jpconstantineau/NRF52-Board/BlueMicro1.x/Images/01.jpg

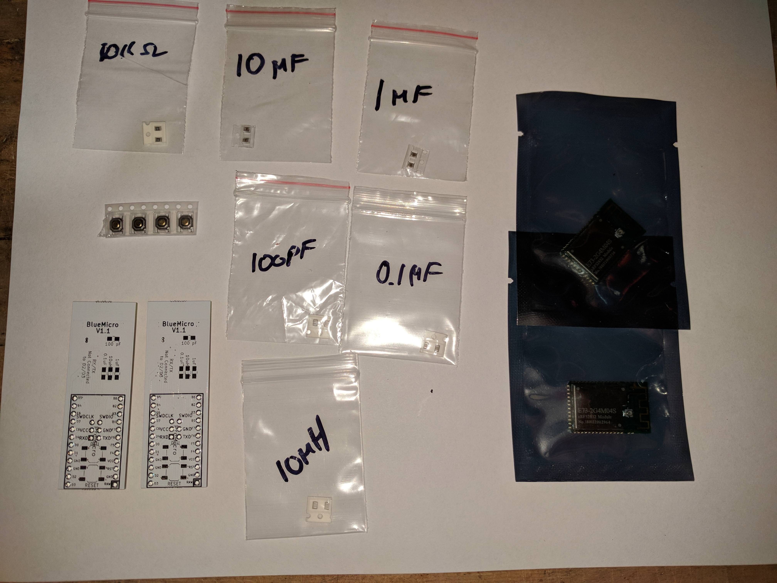
BlueMicro1.x/Images/01.jpg
