jpconstantineau/NRF52-Board/BlueMicro1.x/Images/02.jpg

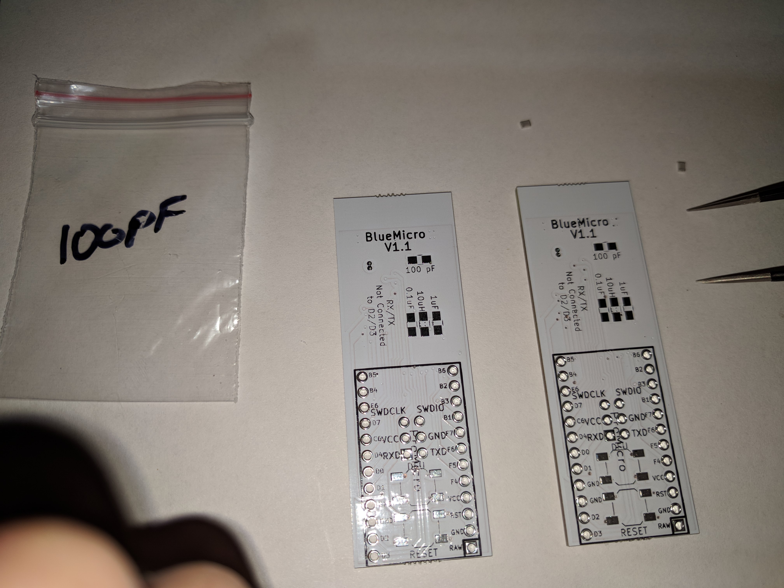
BlueMicro1.x/Images/02.jpg
