jpconstantineau/NRF52-Board/BlueMicro1.x/Images/03.jpg

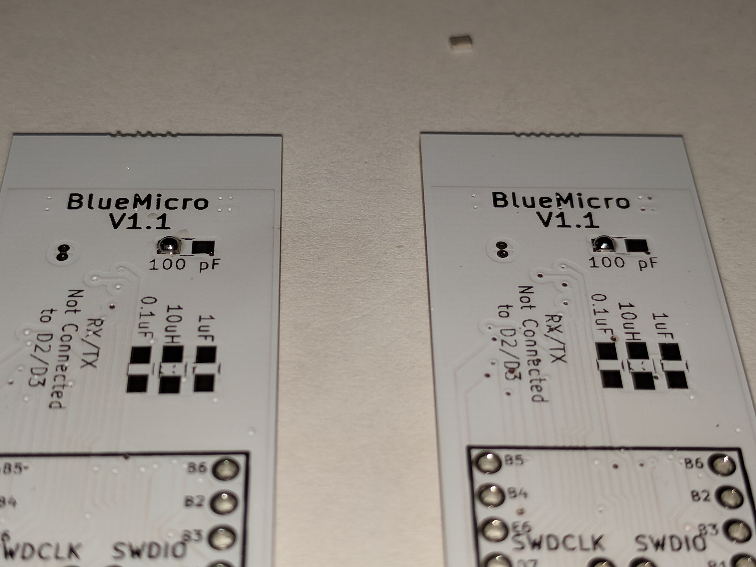
BlueMicro1.x/Images/03.jpg
