jpconstantineau/NRF52-Board/BlueMicro1.x/Images/04.jpg

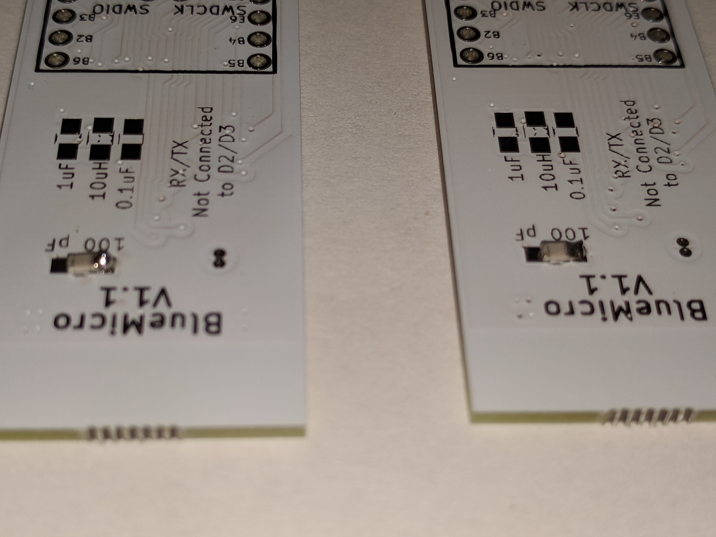
BlueMicro1.x/Images/04.jpg
