jpconstantineau/NRF52-Board/BlueMicro1.x/Images/05.jpg

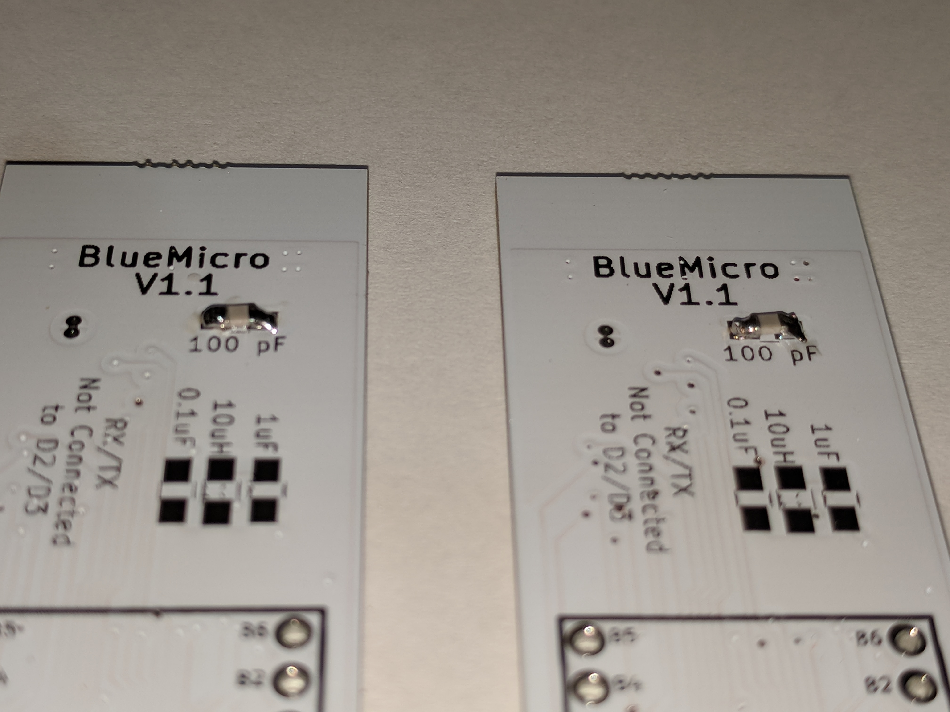
BlueMicro1.x/Images/05.jpg
