jpconstantineau/NRF52-Board/BlueMicro1.x/Images/06.jpg

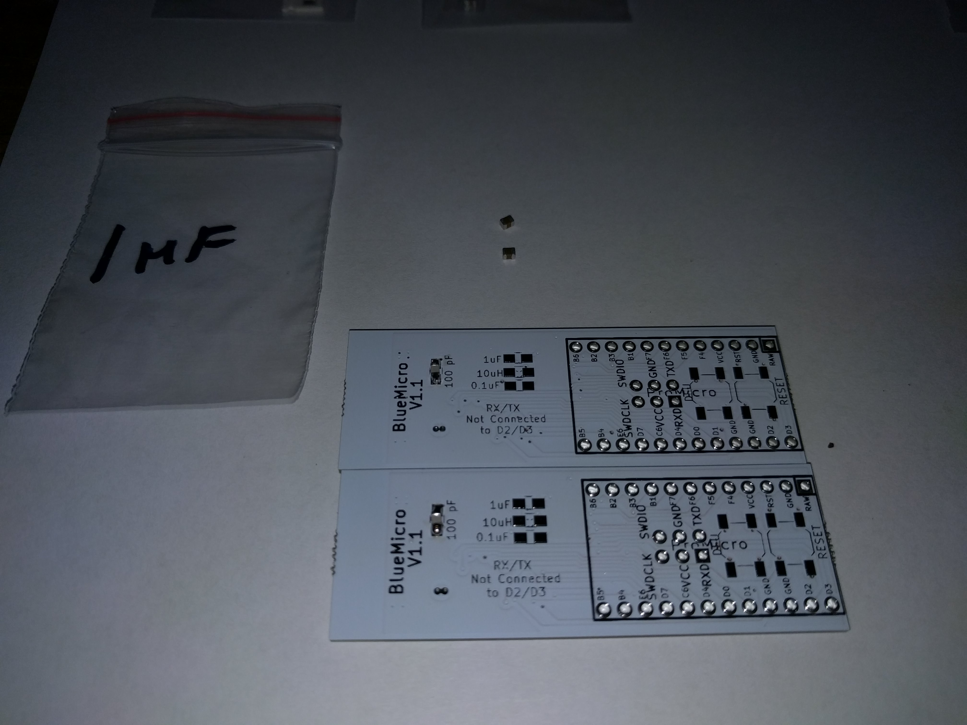
BlueMicro1.x/Images/06.jpg
