jpconstantineau/NRF52-Board/BlueMicro1.x/Images/07.jpg

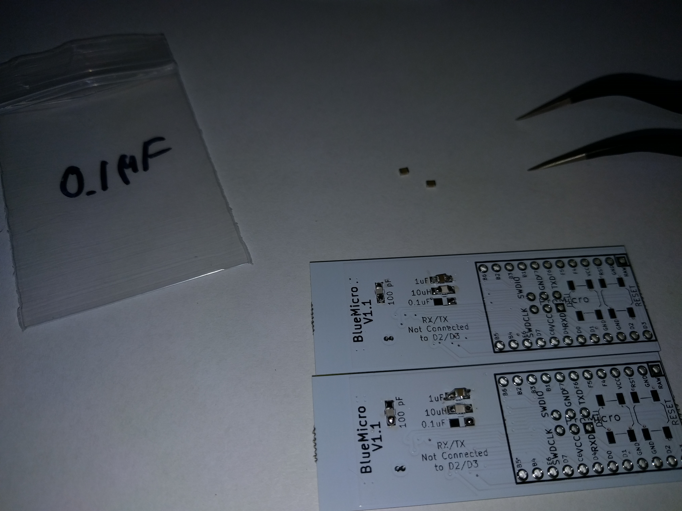
BlueMicro1.x/Images/07.jpg
