jpconstantineau/NRF52-Board/BlueMicro1.x/Images/08.jpg

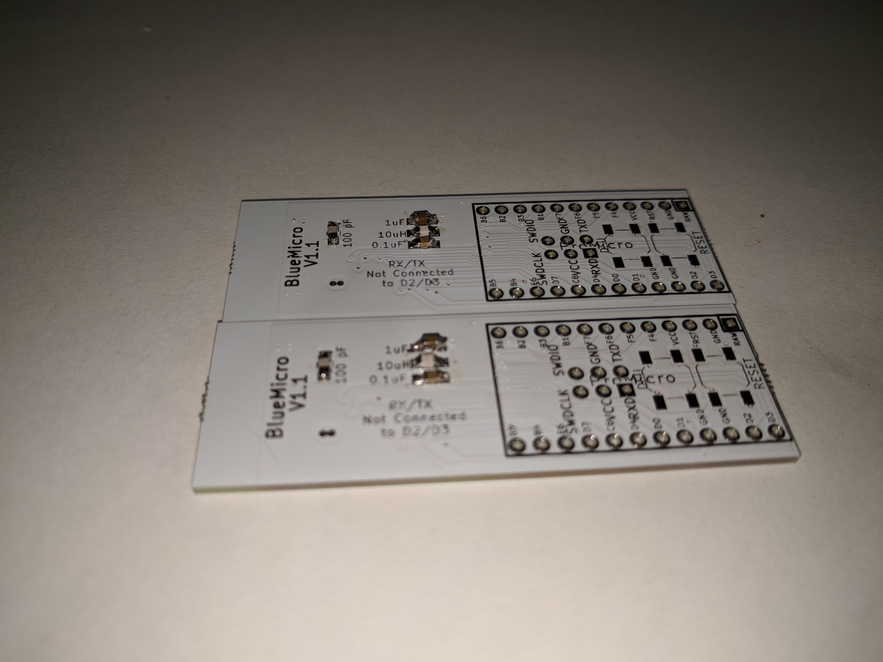
BlueMicro1.x/Images/08.jpg
