jpconstantineau/NRF52-Board/BlueMicro1.x/Images/09.jpg

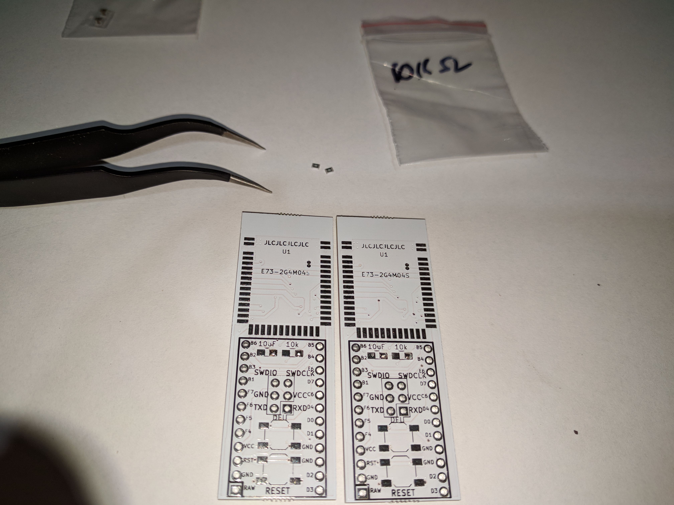
BlueMicro1.x/Images/09.jpg
