jpconstantineau/NRF52-Board/BlueMicro1.x/Images/10.jpg

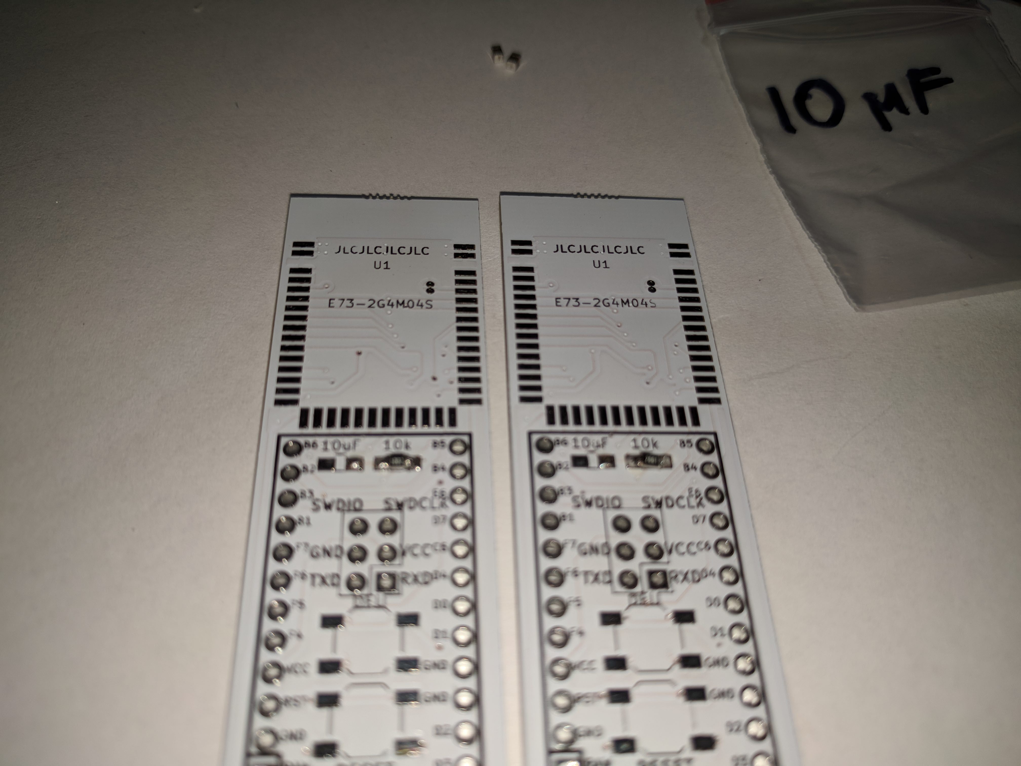
BlueMicro1.x/Images/10.jpg
