jpconstantineau/NRF52-Board/BlueMicro1.x/Images/11.jpg

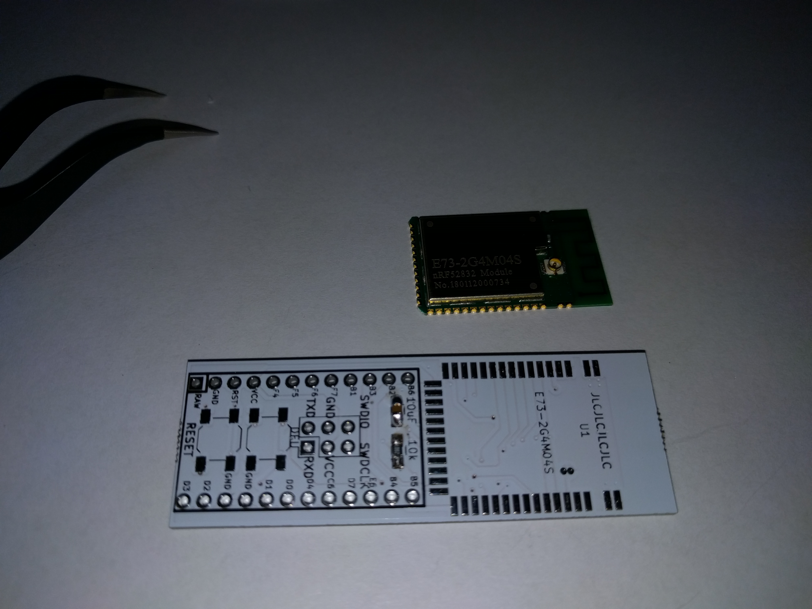
BlueMicro1.x/Images/11.jpg
