jpconstantineau/NRF52-Board/BlueMicro1.x/Images/12.jpg

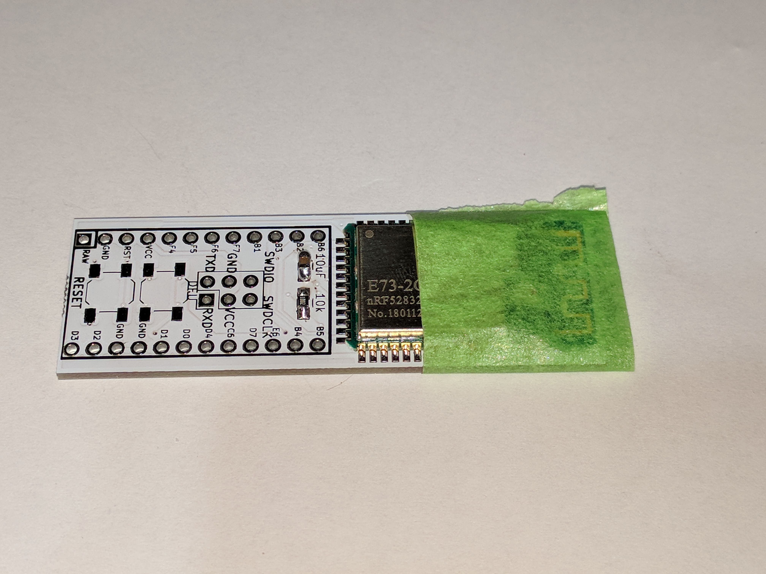
BlueMicro1.x/Images/12.jpg
