jpconstantineau/NRF52-Board/BlueMicro1.x/Images/13.jpg

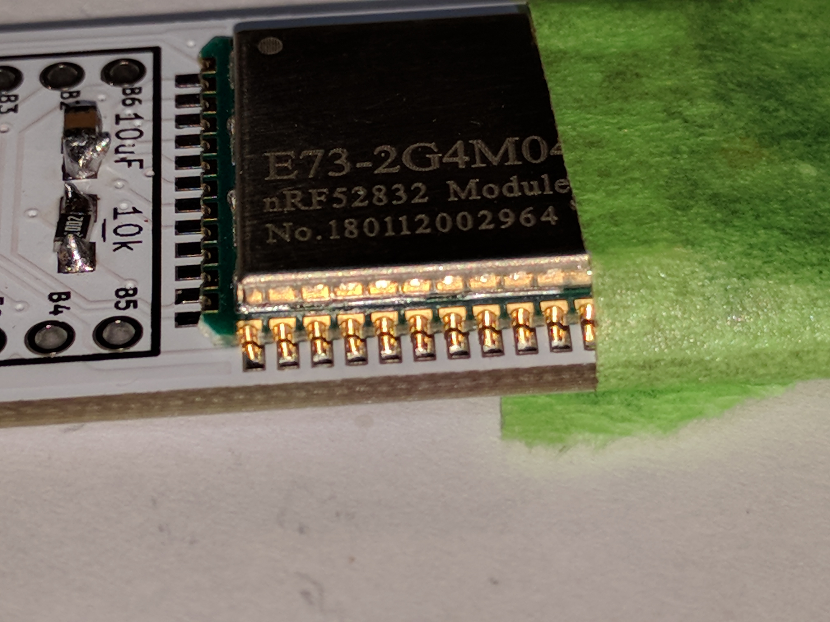
BlueMicro1.x/Images/13.jpg
