jpconstantineau/NRF52-Board/BlueMicro1.x/Images/14.jpg

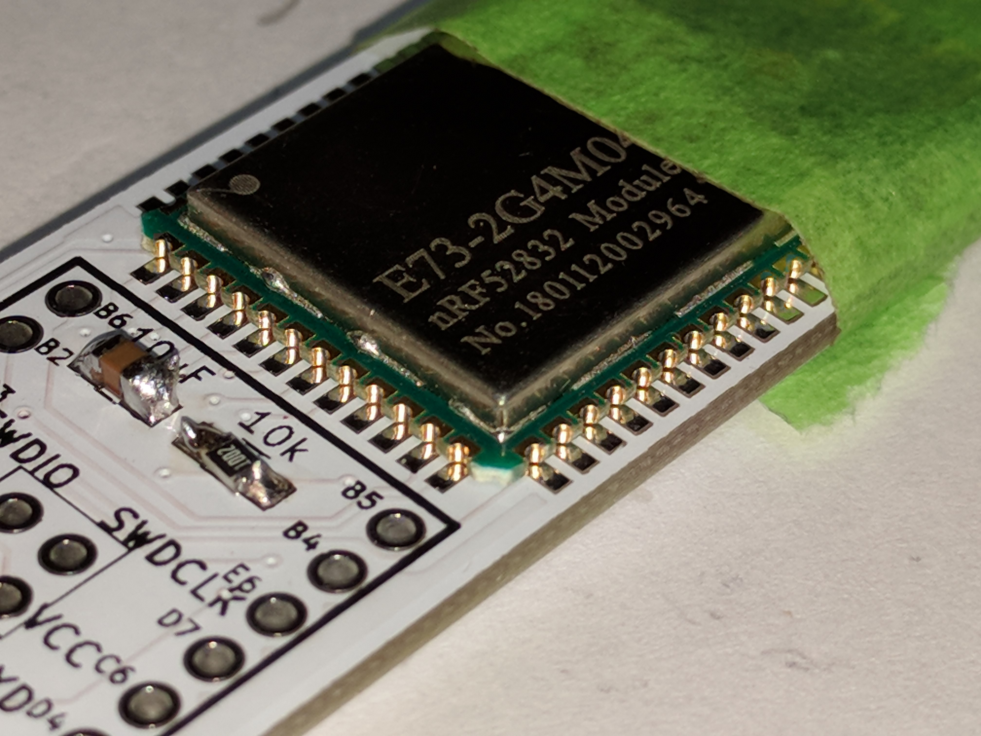
BlueMicro1.x/Images/14.jpg
