jpconstantineau/NRF52-Board/BlueMicro1.x/Images/15.jpg

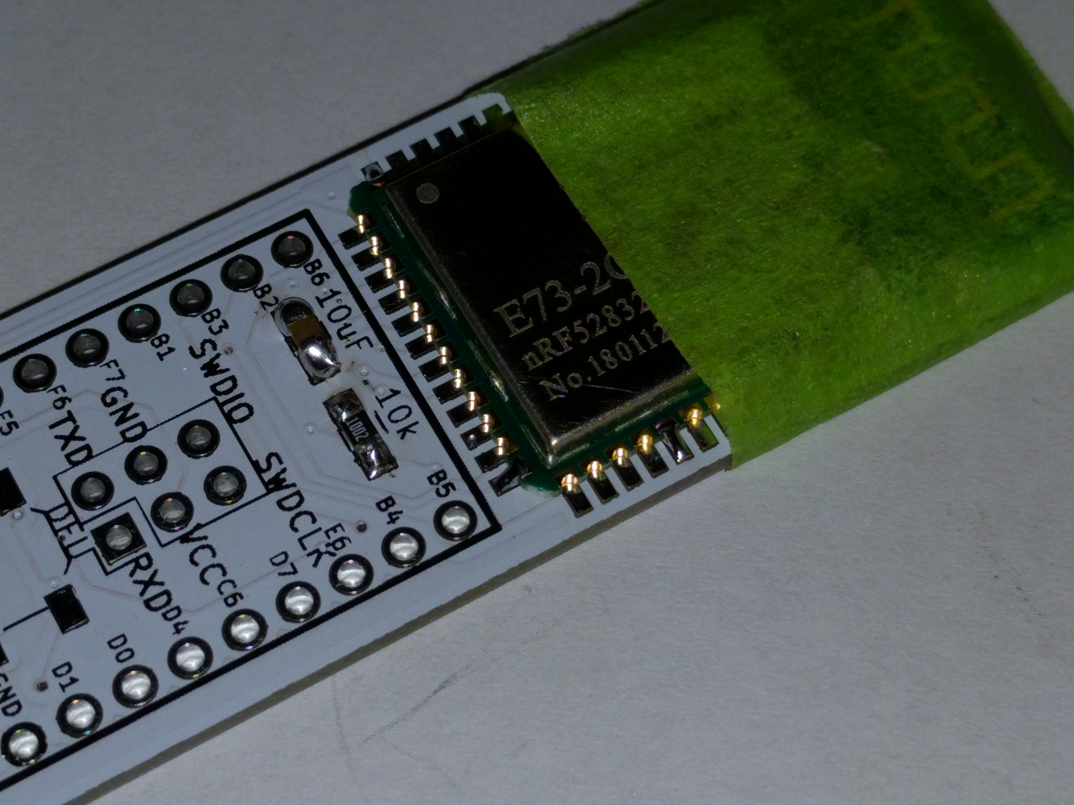
BlueMicro1.x/Images/15.jpg
