jpconstantineau/NRF52-Board/BlueMicro1.x/Images/16.jpg

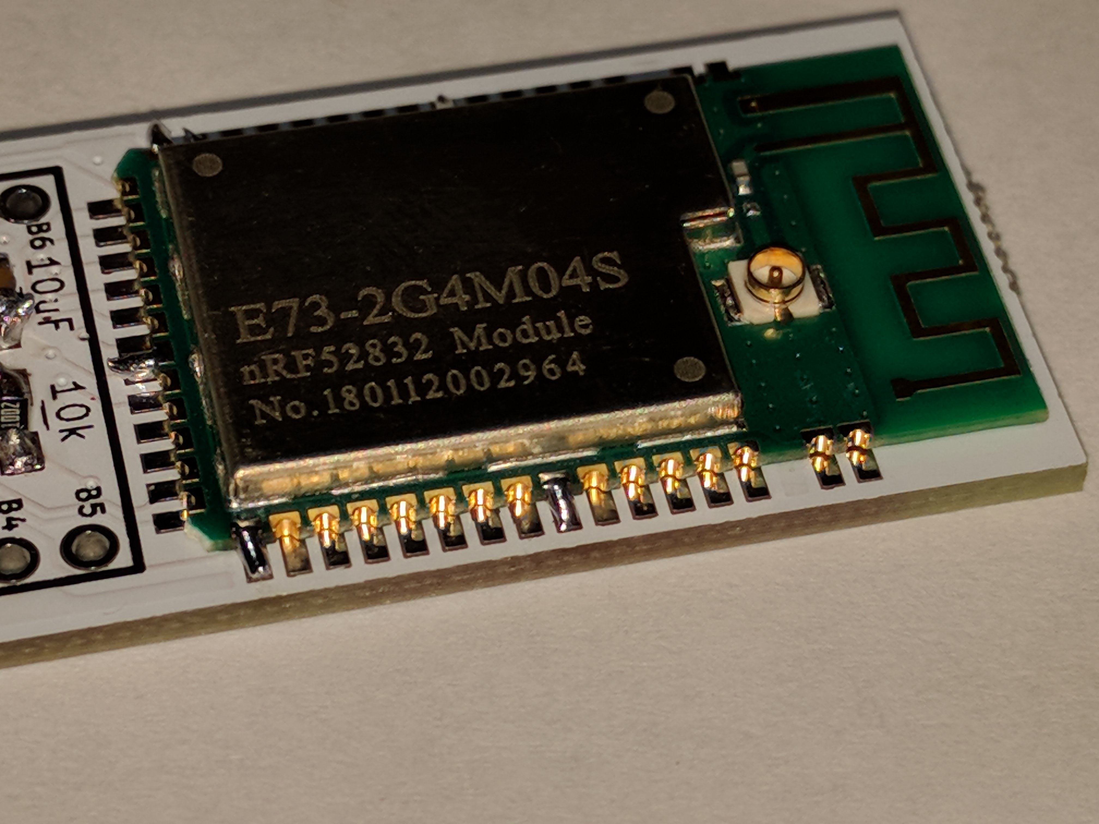
BlueMicro1.x/Images/16.jpg
