jpconstantineau/NRF52-Board/BlueMicro1.x/Images/17.jpg

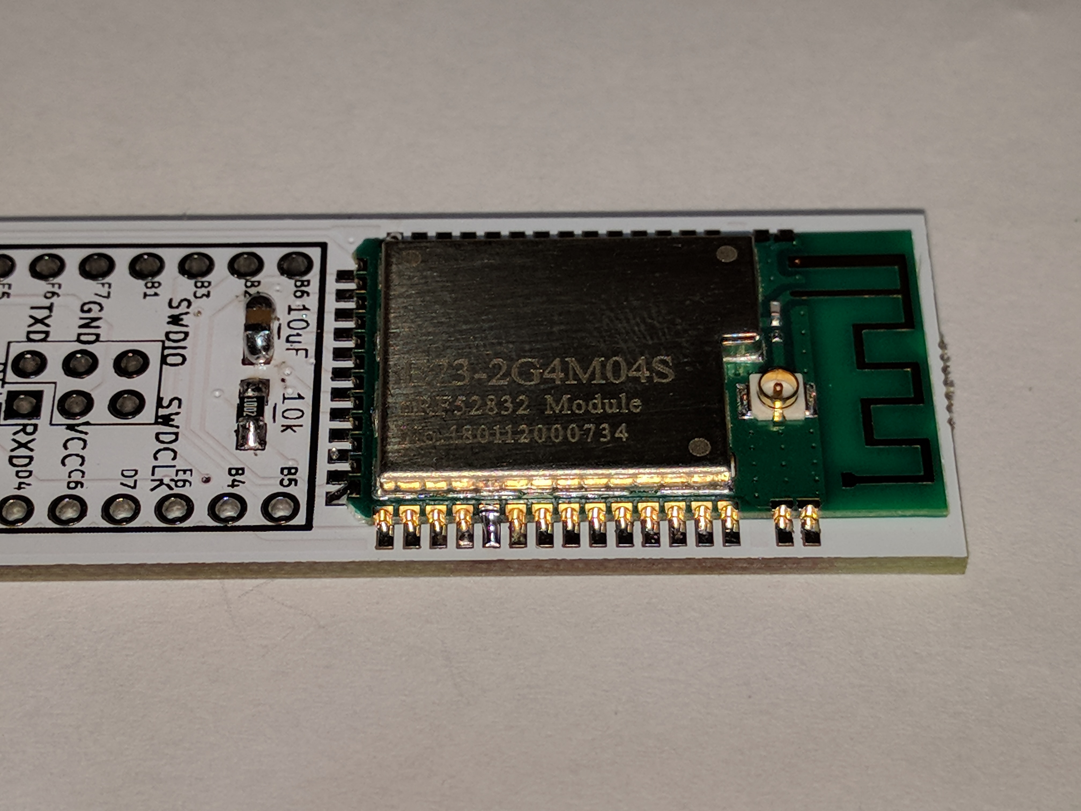
BlueMicro1.x/Images/17.jpg
