jpconstantineau/NRF52-Board/BlueMicro1.x/Images/18.jpg

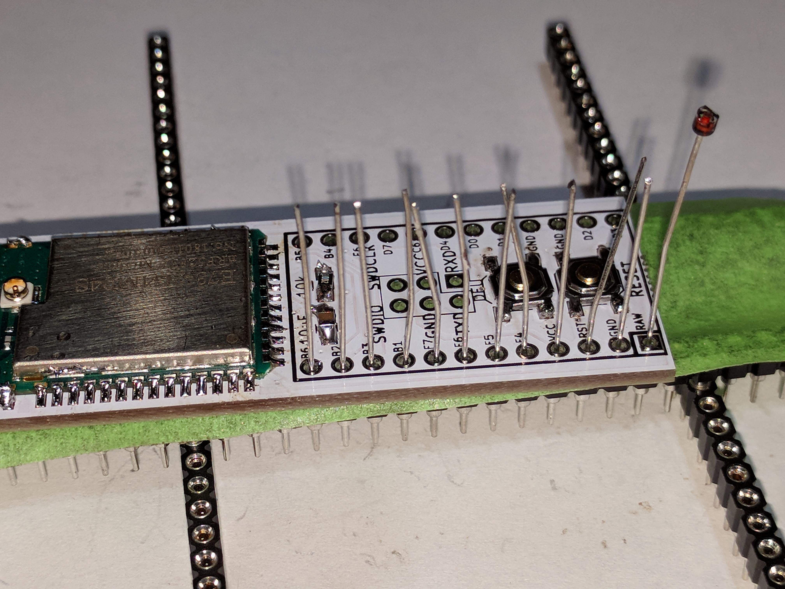
BlueMicro1.x/Images/18.jpg
