jpconstantineau/NRF52-Board/BlueMicro1.x/Images/19.jpg

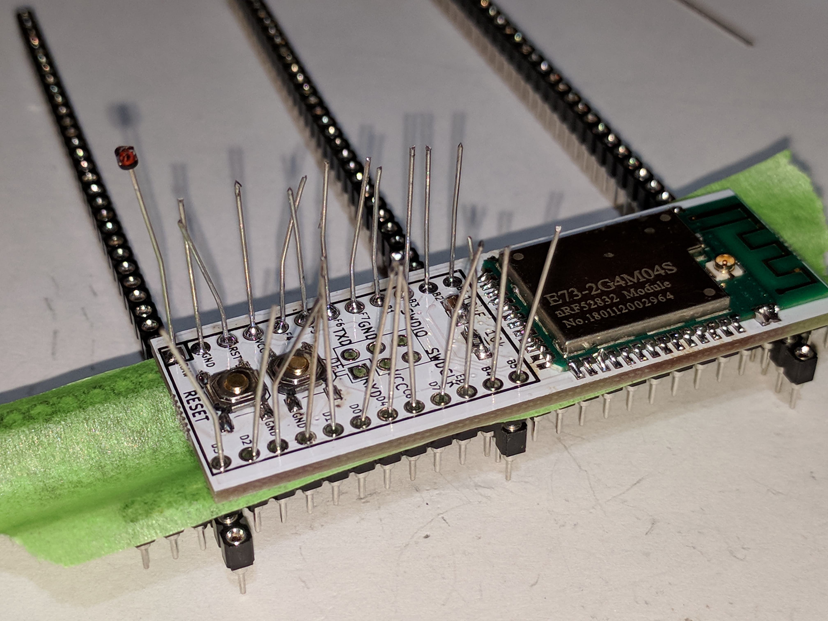
BlueMicro1.x/Images/19.jpg
