jpconstantineau/NRF52-Board/BlueMicro1.x/Images/20.jpg

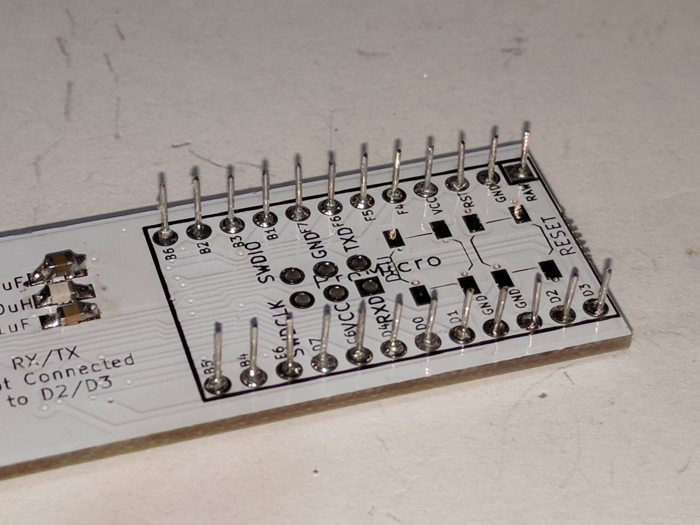
BlueMicro1.x/Images/20.jpg
