jpconstantineau/NRF52-Board/BlueMicro1.x/Images/21.jpg

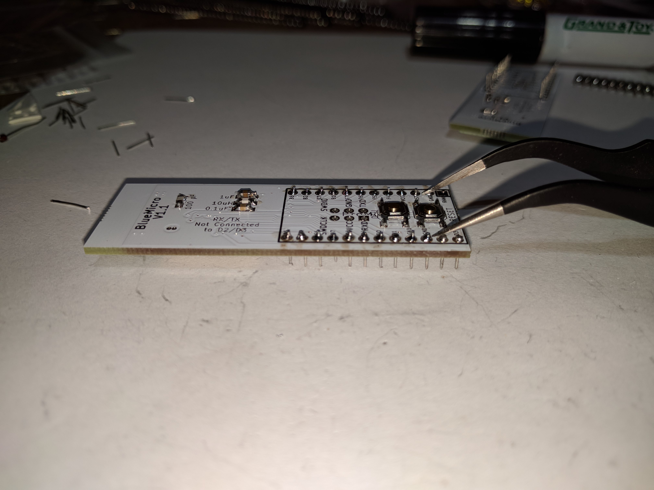
BlueMicro1.x/Images/21.jpg
