jpconstantineau/NRF52-Board/BlueMicro1.x/Images/22.jpg

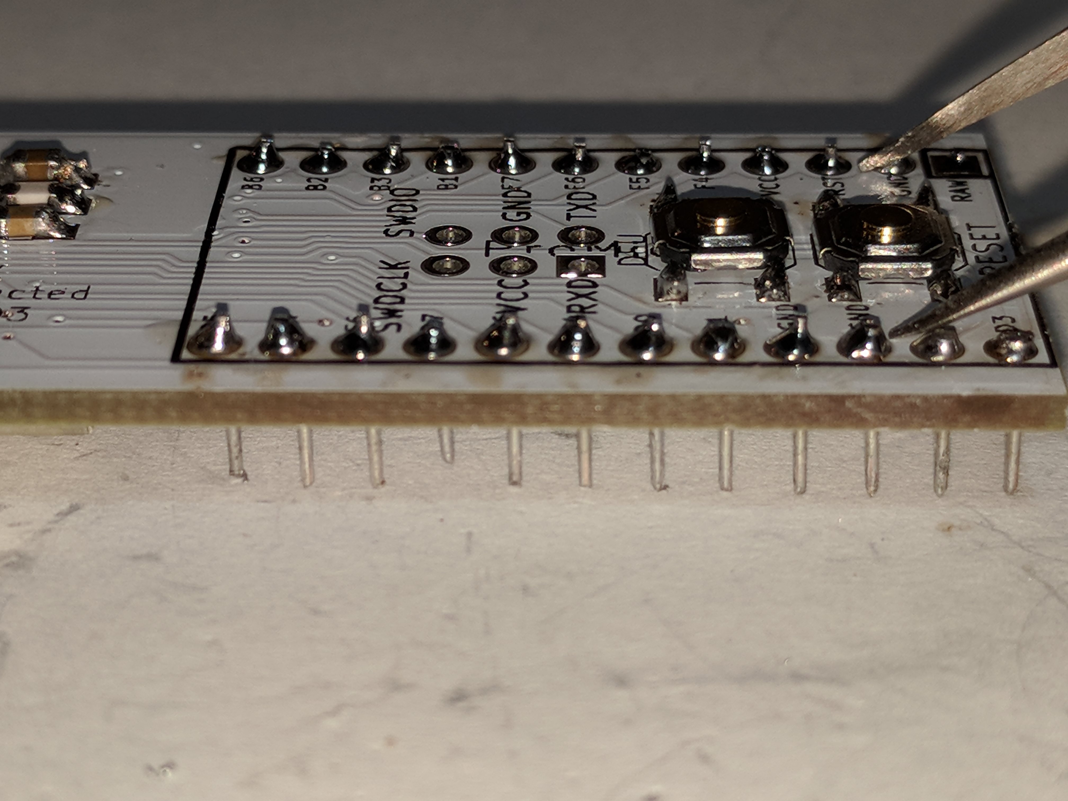
BlueMicro1.x/Images/22.jpg
