jpconstantineau/NRF52-Board/images/BlueMicroSupportedVersions.PNG

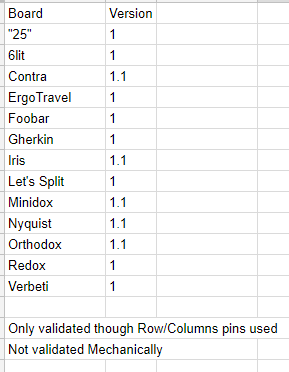
images/BlueMicroSupportedVersions.PNG
