jpconstantineau/NRF52-Board/Reference/CG340GModule.png

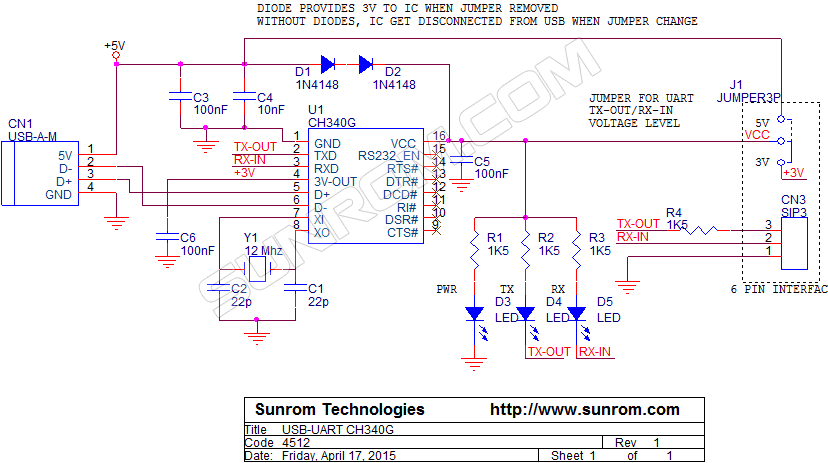
Reference/CG340GModule.png
