jpconstantineau/NRF52-Board/Reference/microcontrollers_BluefruitnRF52Feather_Rev-F.png

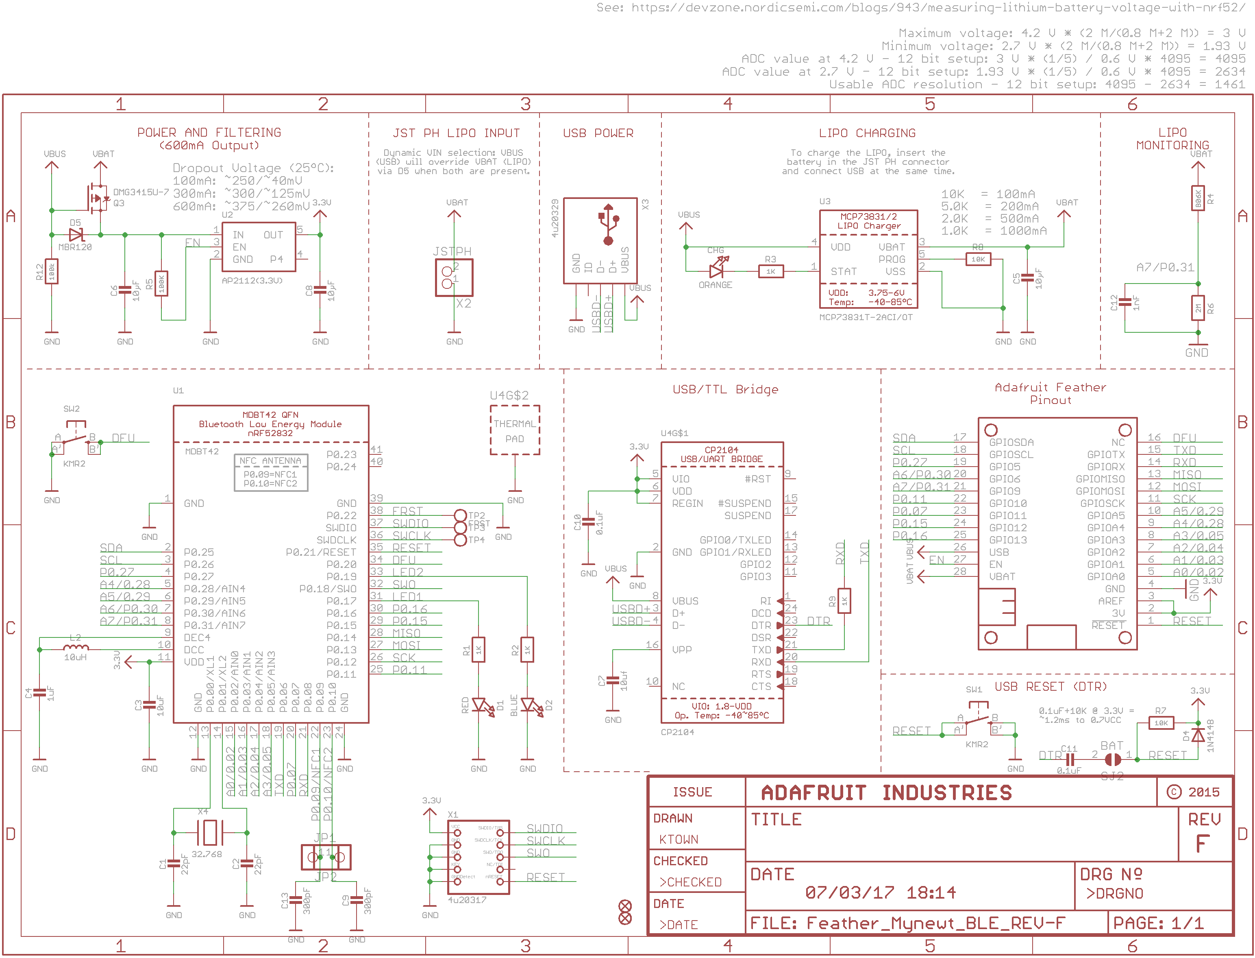
Reference/microcontrollers_BluefruitnRF52Feather_Rev-F.png
