jpconstantineau/NRF52-Board/BlueNano/BlueNano 1.0/NRF52832 Base.pdf

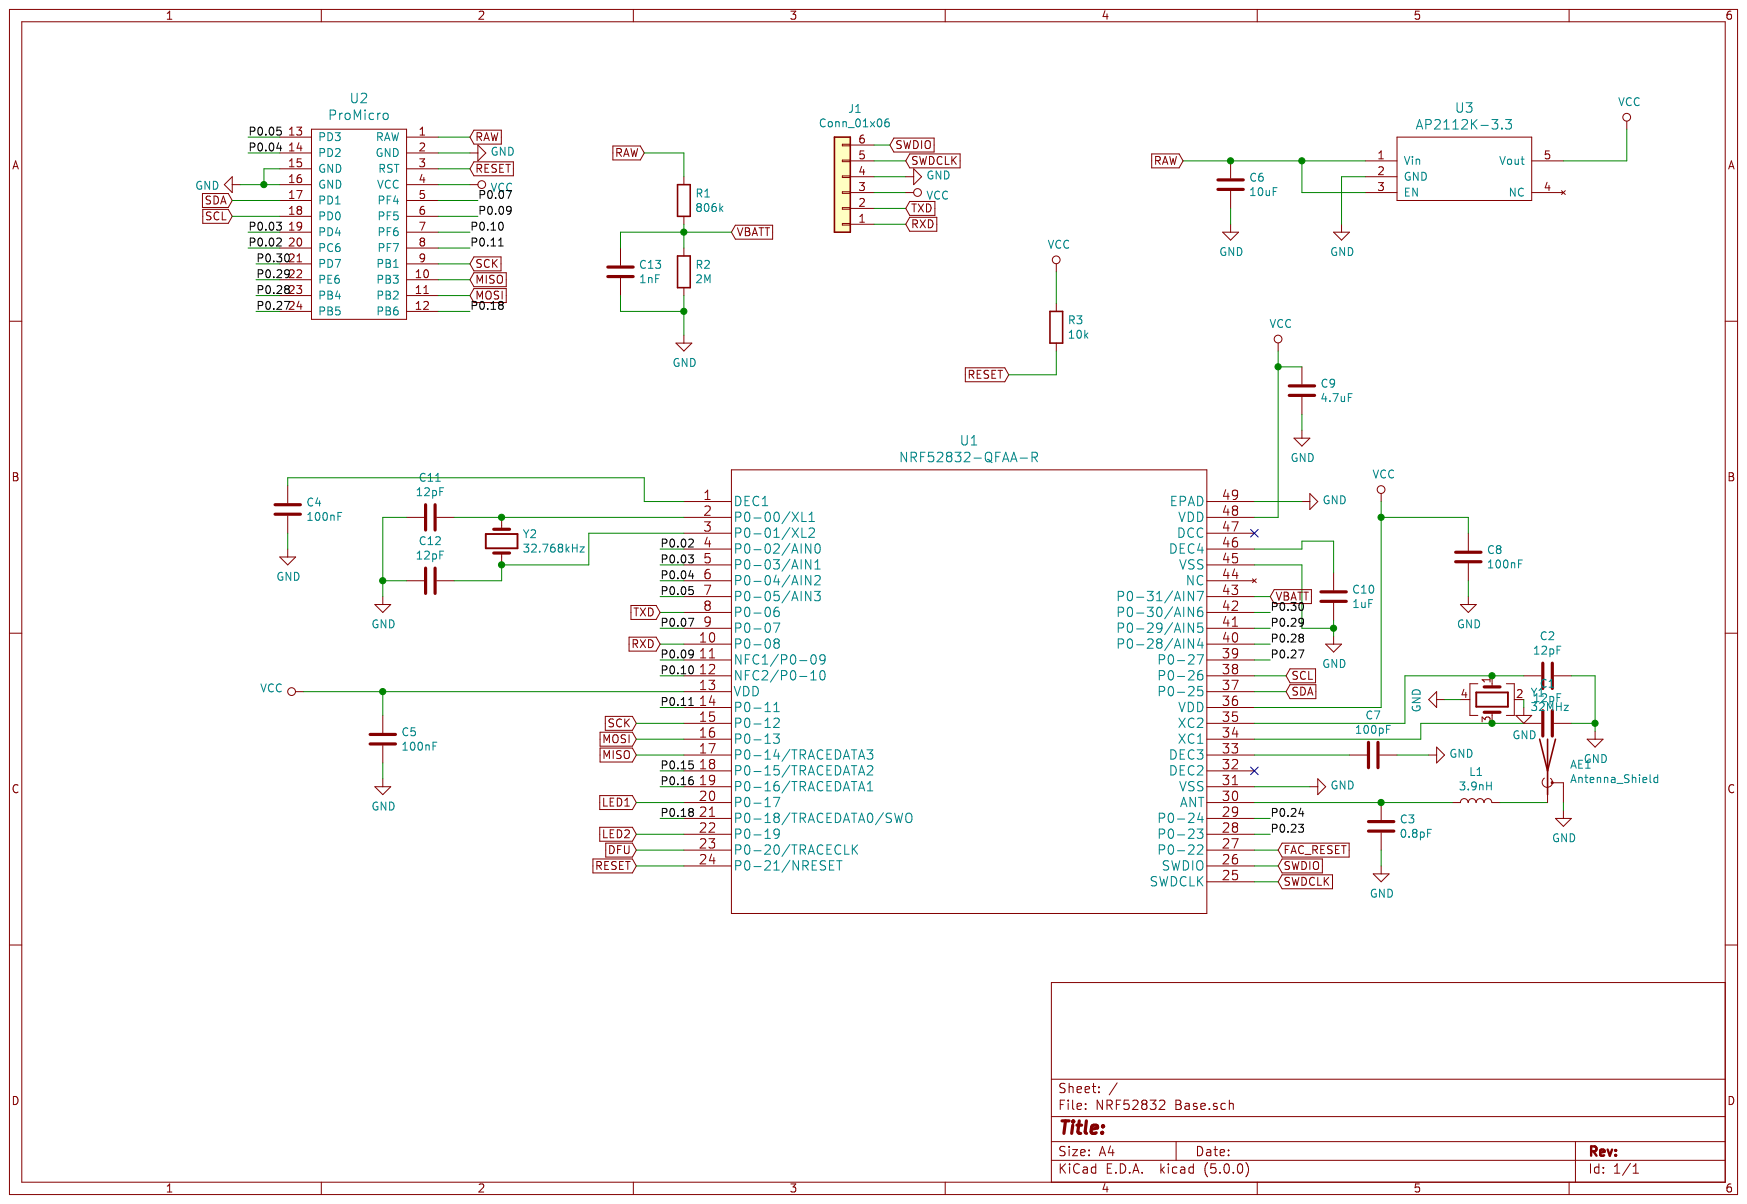
[picture p49: page 1]
