jpconstantineau/NRF52-Board/BlueMacro840/BlueMacro840_V1.0_Schematic.pdf

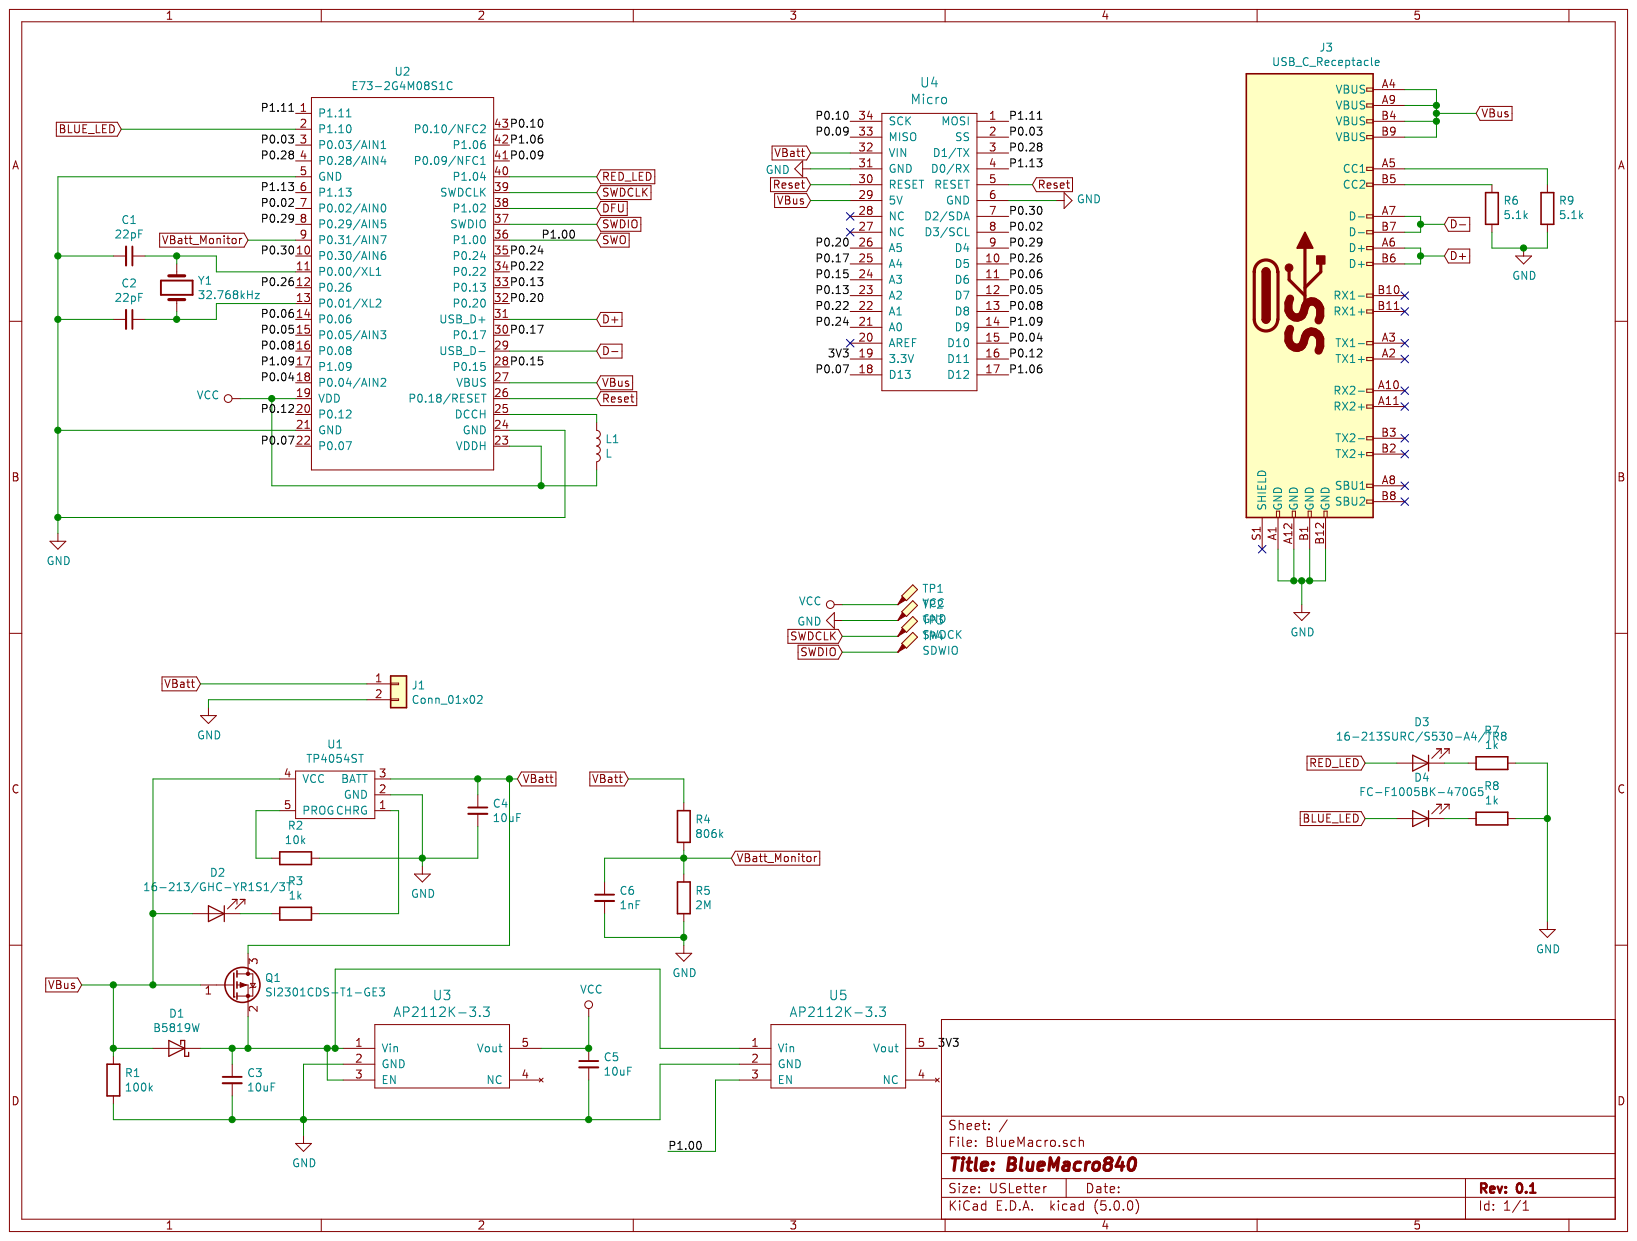
[picture p50: page 1]
